sudo-apt-install-tap/ZEUS/Images/3ding cart.png

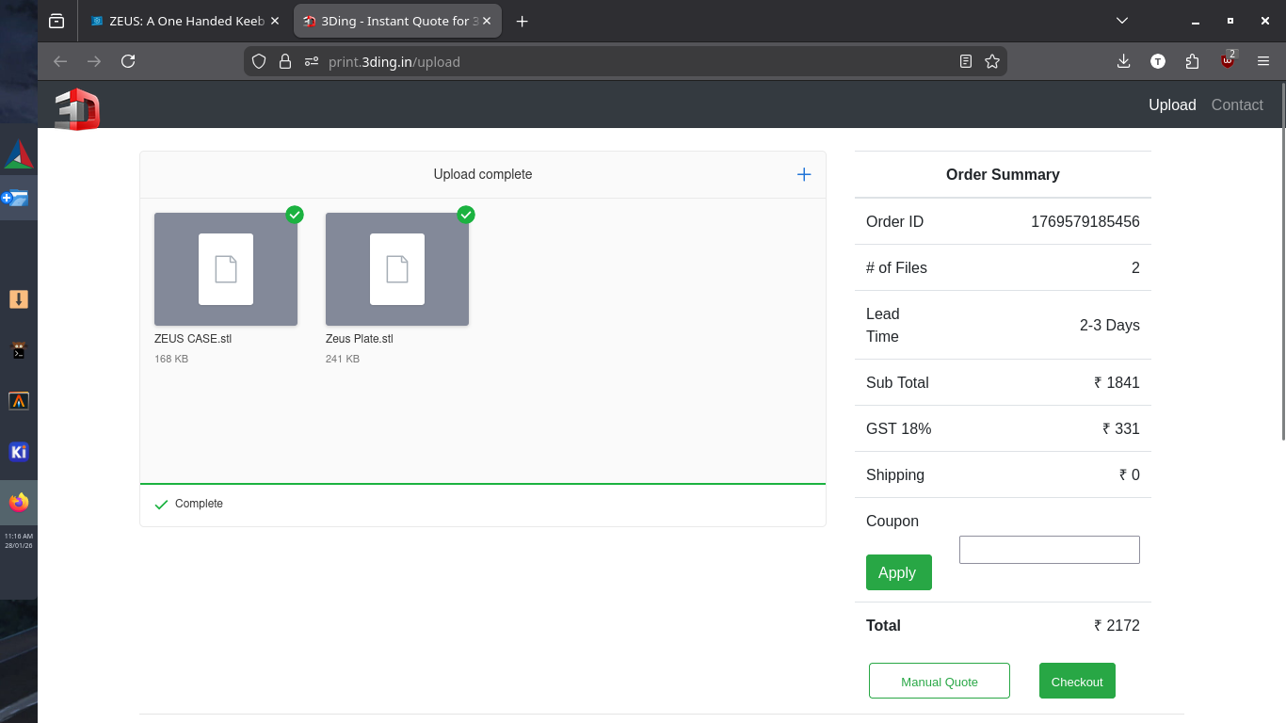
Images/3ding cart.png
