sudo-apt-install-tap/ZEUS/Images/JLC CART.png

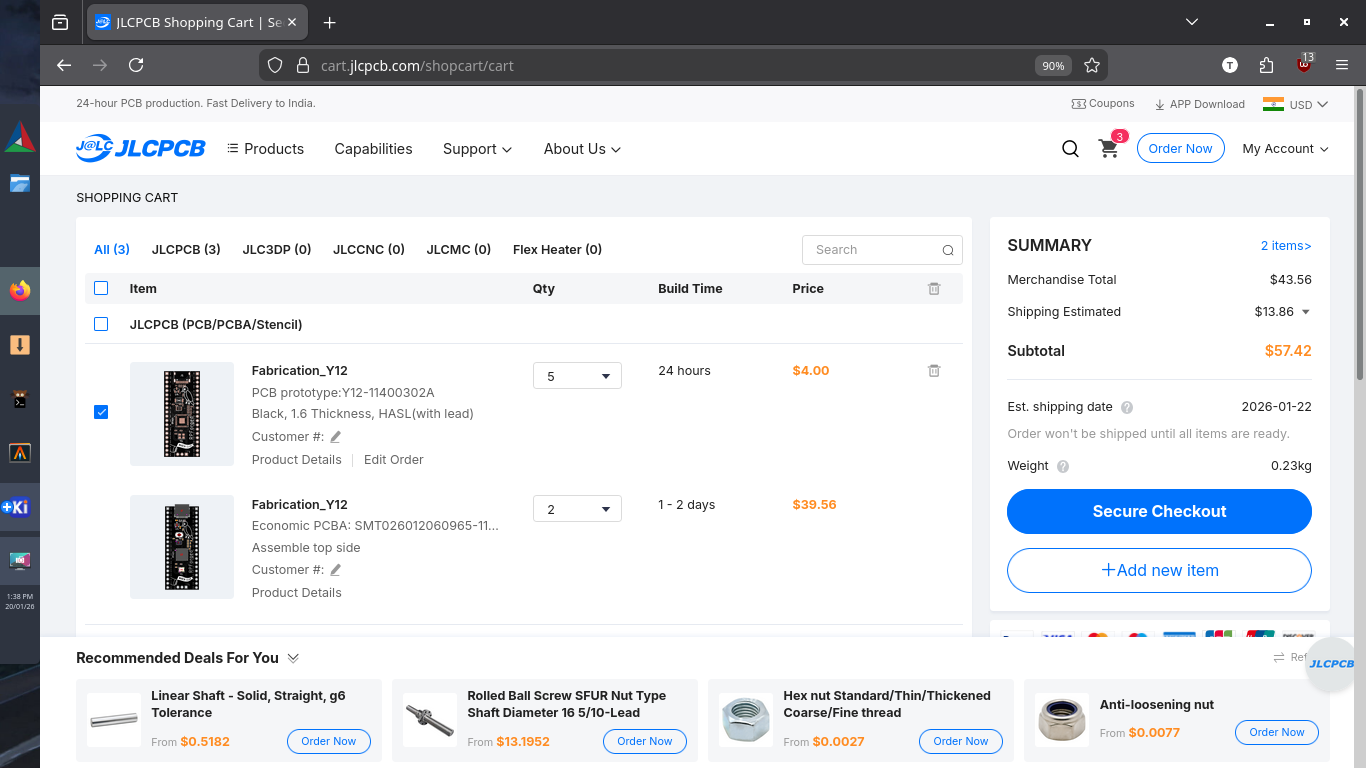
Images/JLC CART.png
