sudo-apt-install-tap/ZEUS/Images/Matrix Routing.png

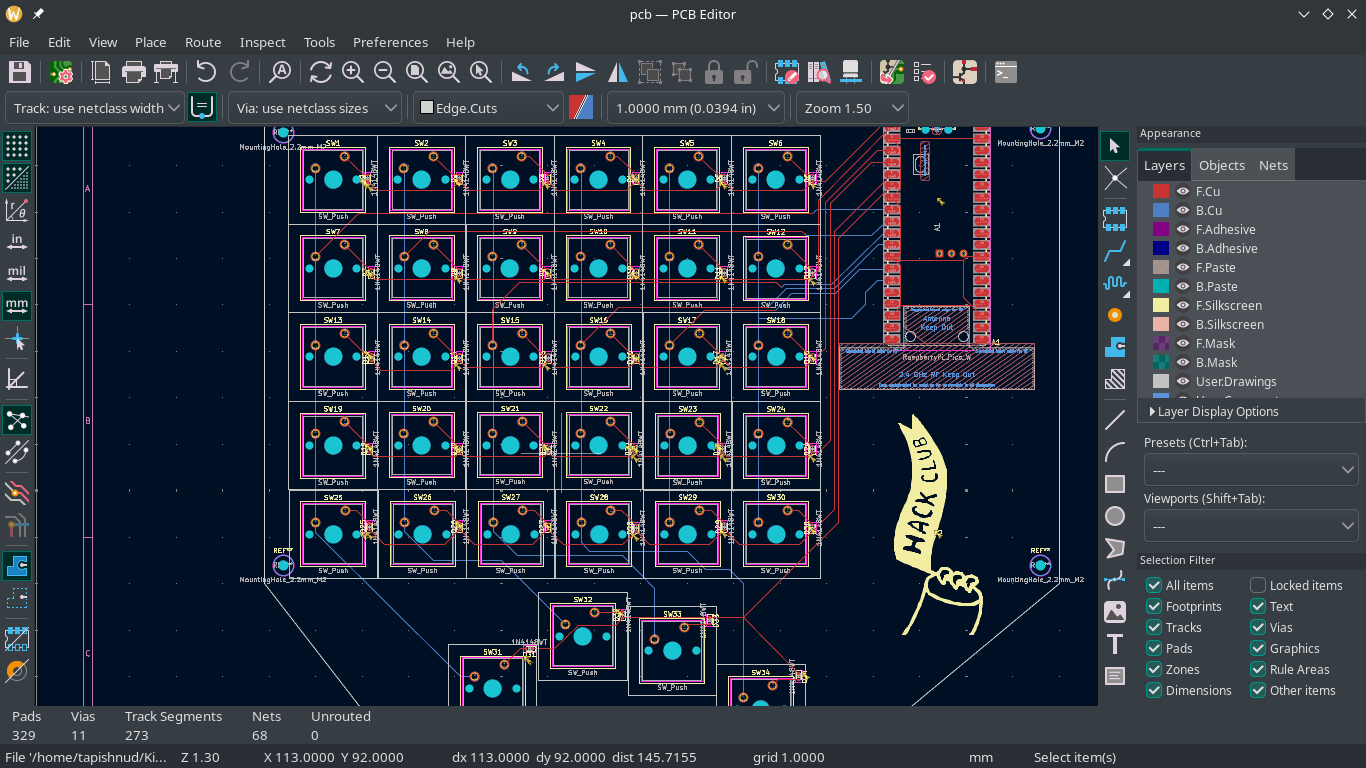
Images/Matrix Routing.png
