sudo-apt-install-tap/ZEUS/Images/PCB Routing 1.png

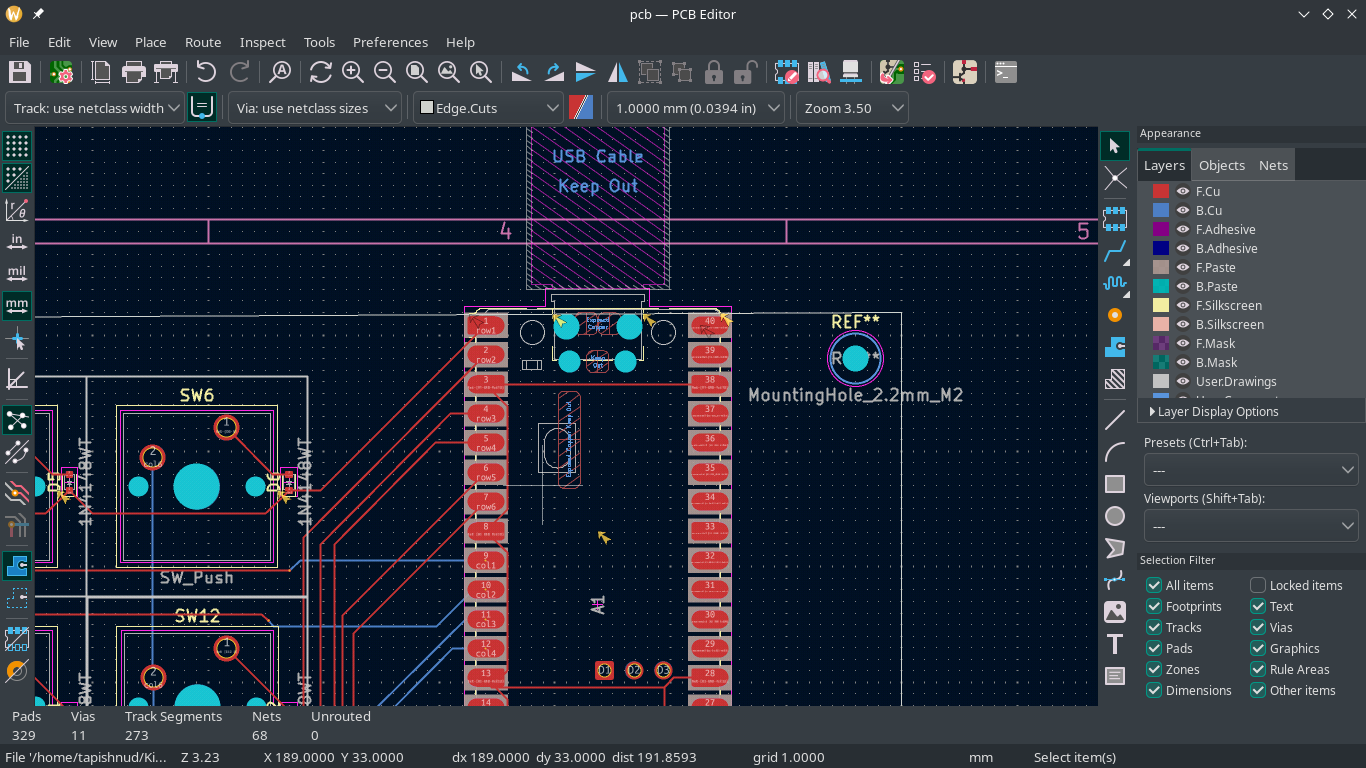
Images/PCB Routing 1.png
