sudo-apt-install-tap/ZEUS/Images/PCB Routing 2.png

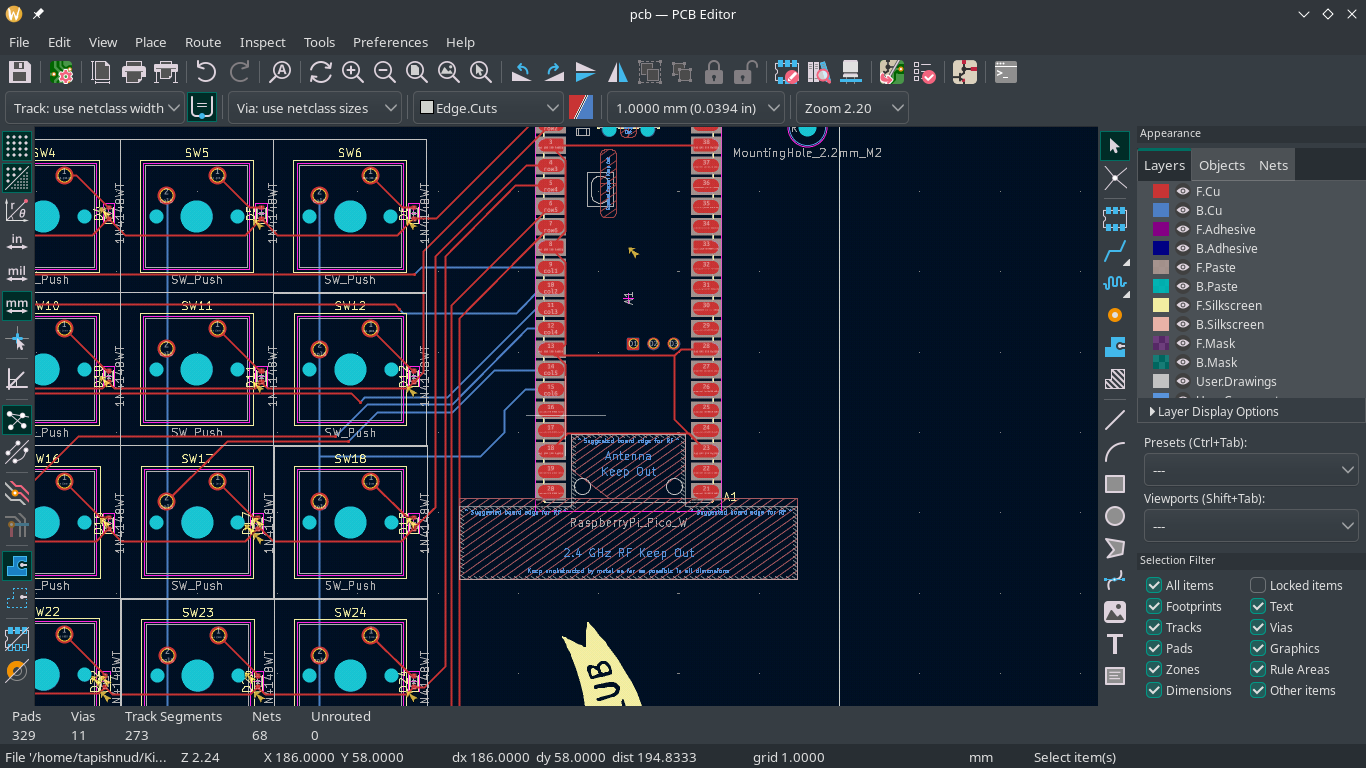
Images/PCB Routing 2.png
